martinzosr/Octoprint-status-dashboard/Pictures/20221001_145310.jpg

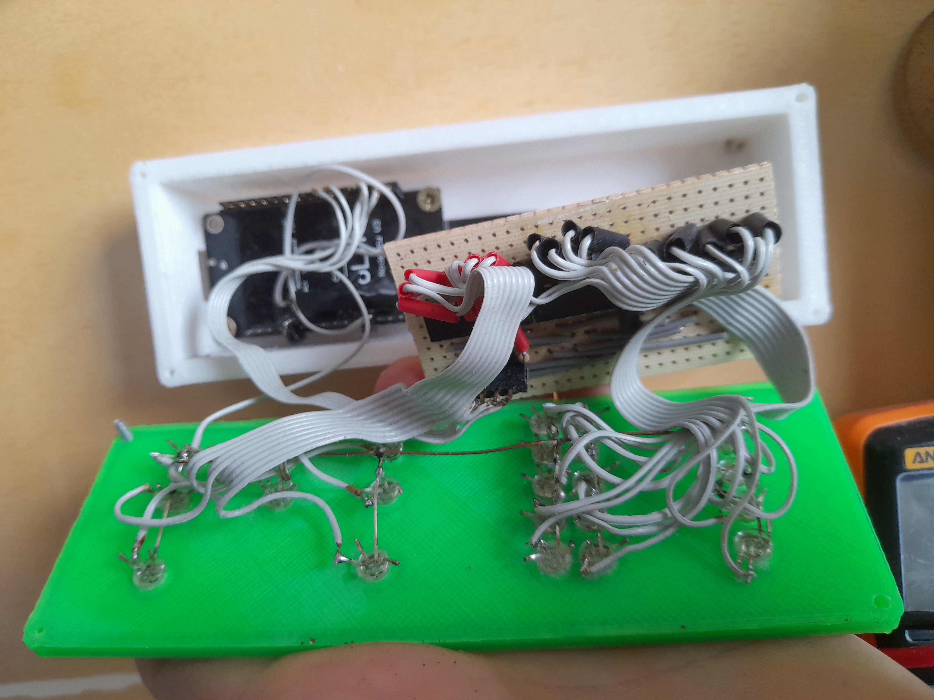
Pictures/20221001_145310.jpg
